limingjie/Smart-LED-Flashlight-CH32V003/schematic/CH32V003_SGM3732_Portable_LED/CH32V003_SGM3732_Portable_LED.kicad_sch

## KiCad design schematic/CH32V003_SGM3732_Portable_LED/CH32V003_SGM3732_Portable_LED.kicad_sch (2025-09-14)

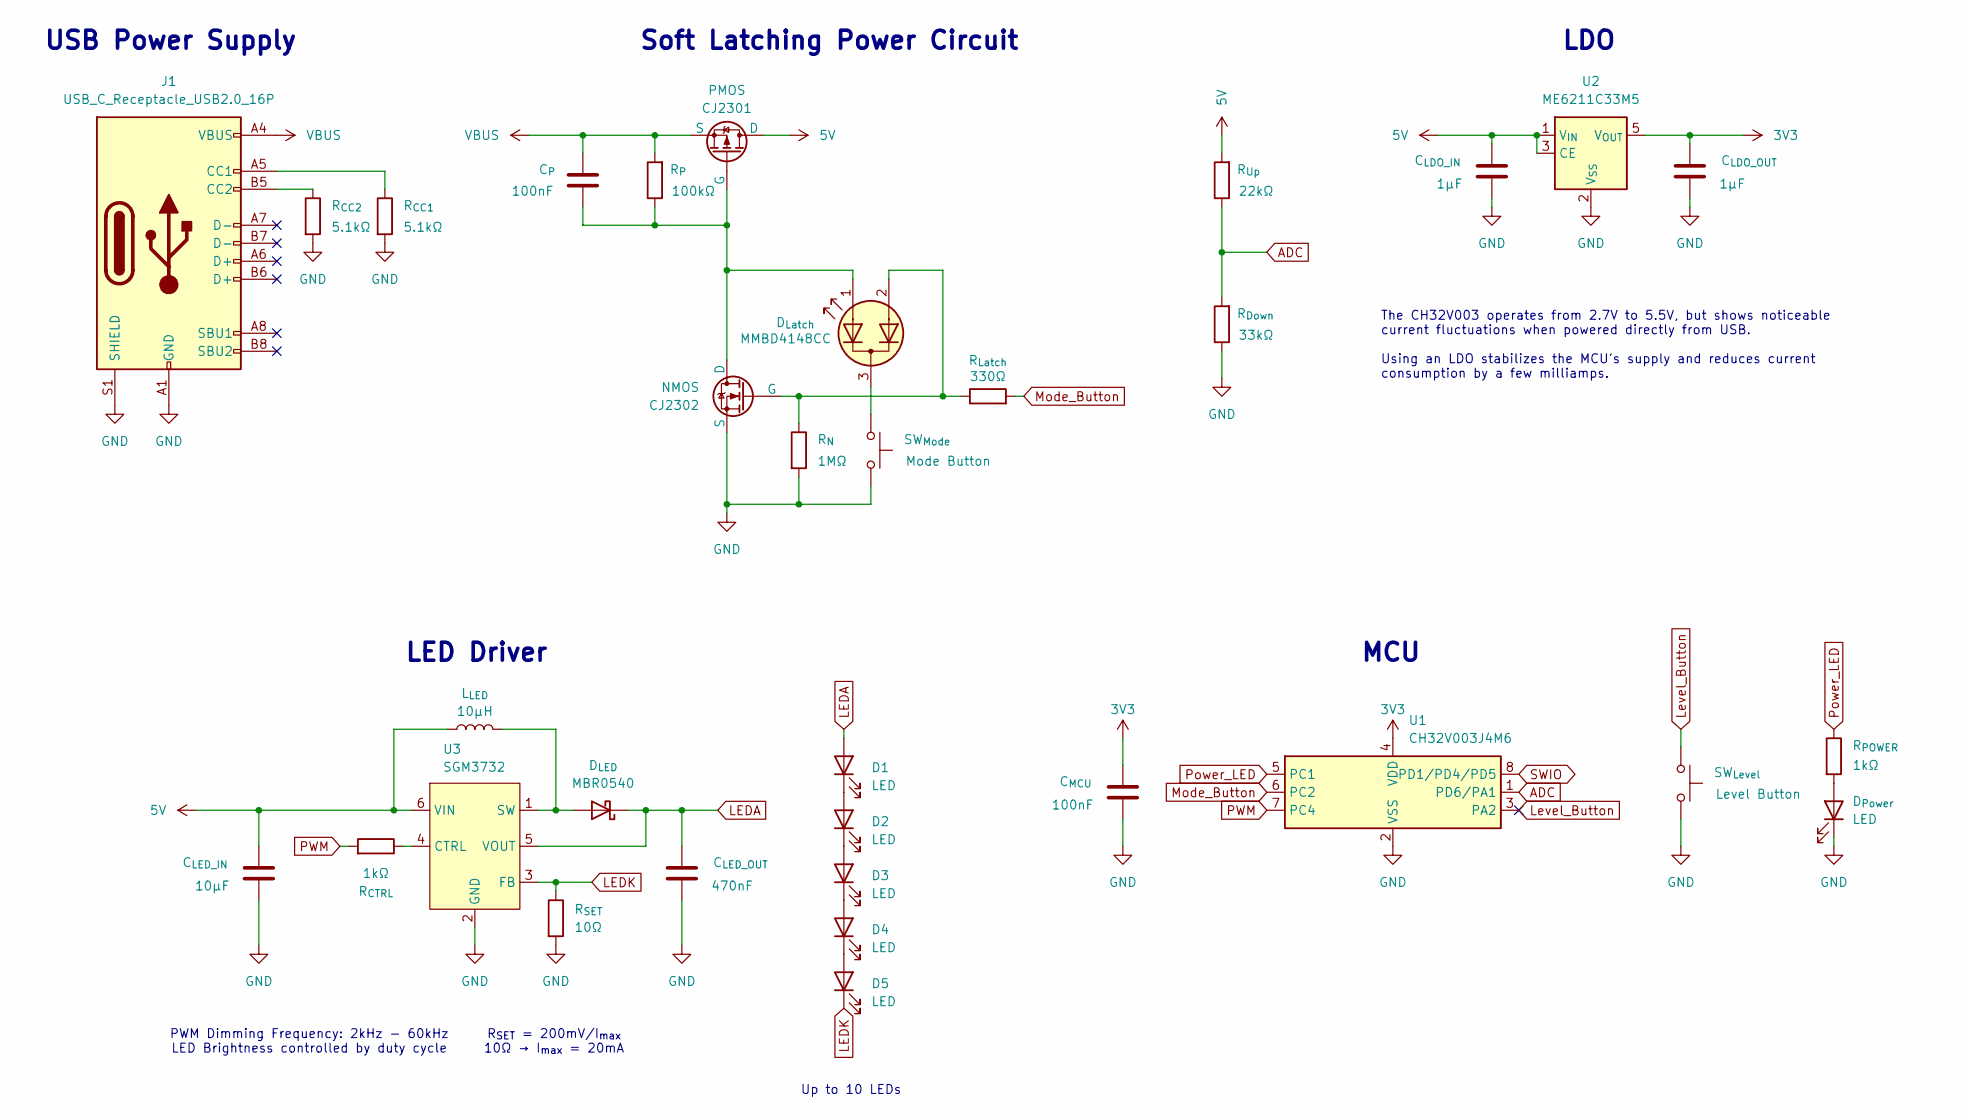
[picture p5: schematic CH32V003_SGM3732_Portable_LED.kicad_sch]

Parts:
C_{LDO_IN}: 1µF
C_{LDO_OUT}: 1µF
C_{LED_IN}: 10µF
C_{LED_OUT}: 470nF
C_{MCU}: 100nF
C_{P}: 100nF
D1, D2, D3, D4, D5: LED
D_{LED}: MBR0540
D_{Latch}: MMBD4148CC
D_{Power}: LED
J1: USB_C_Receptacle_USB2.0_16P
L_{LED}: 10µH
NMOS: CJ2302
PMOS: CJ2301
R_{CC1}, R_{CC2}: 5.1kΩ
R_{CTRL}: 1kΩ
R_{Down}: 33kΩ
R_{Latch}: 330Ω
R_{N}: 1MΩ
R_{POWER}: 1kΩ
R_{P}: 100kΩ
R_{SET}: 10Ω
R_{Up}: 22kΩ
SW_{Level}: Level Button
SW_{Mode}: Mode Button
U1: CH32V003J4M6; JEITA_SOIC-8_3.9x4.9mm_P1.27mm
U2: ME6211C33M5; SOT-23-5
U3: SGM3732

Connections:
3V3: C_{LDO_OUT}.1, C_{MCU}.1, U1.4 (VDD), U2.5 (V_{OUT})
5V: C_{LDO_IN}.1, C_{LED_IN}.1, L_{LED}.1, PMOS.1 (D), R_{Up}.2, U2.1 (V_{IN}), U2.3 (CE), U3.6 (VIN)
ADC: R_{Down}.2, R_{Up}.1, U1.1 (PD6/PA1)
GND: C_{LDO_IN}.2, C_{LDO_OUT}.2, C_{LED_IN}.2, C_{LED_OUT}.2, C_{MCU}.2, D_{Power}.1 (K), J1.A1 (GND), J1.A12 (GND), J1.B1 (GND), J1.B12 (GND), J1.S1 (SHIELD), NMOS.3 (S), R_{CC1}.2, R_{CC2}.2, R_{Down}.1, R_{N}.2, R_{SET}.2, SW_{Level}.1, SW_{Mode}.1, U1.2 (VSS), U2.2 (V_{SS}), U3.2 (GND)
LEDA: C_{LED_OUT}.1, D1.2 (A), D_{LED}.1 (K), U3.5 (VOUT)
LEDK: D5.1 (K), R_{SET}.1, U3.3 (FB)
Level_Button: SW_{Level}.2, U1.3 (PA2)
Mode_Button: R_{Latch}.2, U1.6 (PC2)
unnamed: C_{P}.2, D_{Latch}.1 (A1), NMOS.1 (D), PMOS.2 (G), R_{P}.1
unnamed: D1.1 (K), D2.2 (A)
unnamed: D2.1 (K), D3.2 (A)
unnamed: D3.1 (K), D4.2 (A)
unnamed: D4.1 (K), D5.2 (A)
unnamed: D_{LED}.2 (A), L_{LED}.2, U3.1 (SW)
unnamed: D_{Latch}.2 (A2), NMOS.2 (G), R_{Latch}.1, R_{N}.1
unnamed: D_{Latch}.3 (K), SW_{Mode}.2
unnamed: D_{Power}.2 (A), R_{POWER}.2
unnamed: J1.A5 (CC1), R_{CC1}.1
unnamed: J1.B5 (CC2), R_{CC2}.1
unnamed: R_{CTRL}.1, U3.4 (CTRL)
PWM: R_{CTRL}.2, U1.7 (PC4)
Power_LED: R_{POWER}.1, U1.5 (PC1)
SWIO: U1.8 (PD1/PD4/PD5)
VBUS: C_{P}.1, J1.A4 (VBUS), J1.A9 (VBUS), J1.B4 (VBUS), J1.B9 (VBUS), PMOS.3 (S), R_{P}.2

Notes on the sheet:
MCU
Up to 10 LEDs
Soft Latching Power Circuit
LDO
LED Driver
R_{SET} = 200mV/I_{max} 10Ω → I_{max} = 20mA
The CH32V003 operates from 2.7V to 5.5V, but shows noticeable current fluctuations when powered directly from USB. Using an LDO stabilizes the MCU's supply and reduces current consumption by a few milliamps.
PWM Dimming Frequency: 2kHz - 60kHz LED Brightness controlled by duty cycle
USB Power Supply
